moneytech/ZX1541-Interface/files_found_on_the_internet/Pictures/0001a.jpg

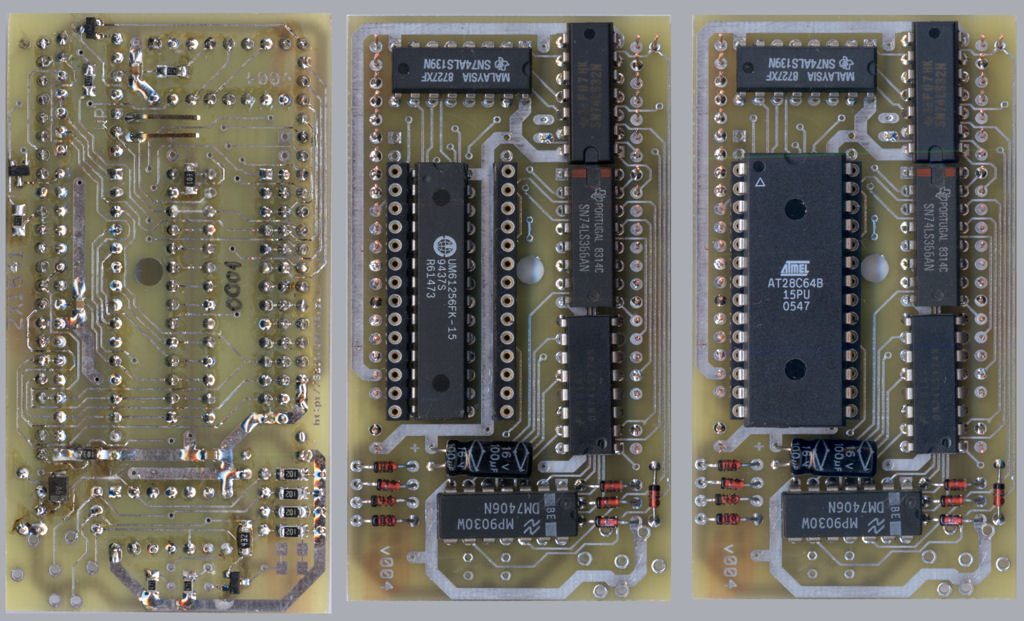
files_found_on_the_internet/Pictures/0001a.jpg
