moneytech/ZX1541-Interface/files_found_on_the_internet/Pictures/0003b.jpg

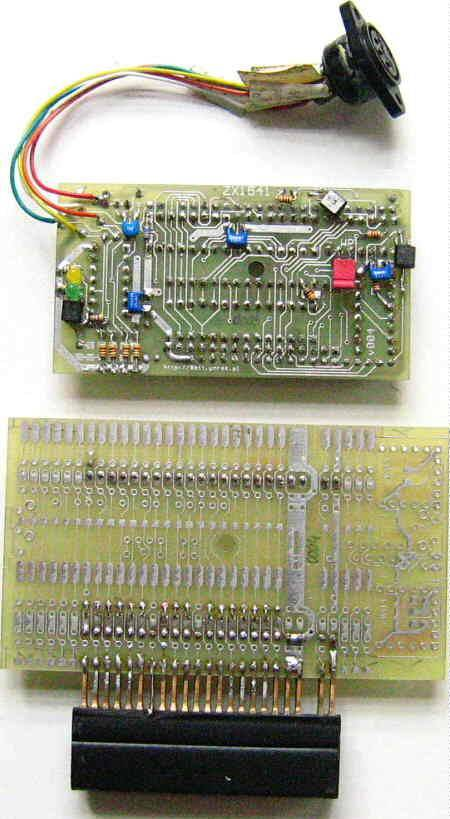
files_found_on_the_internet/Pictures/0003b.jpg
