moneytech/ZX1541-Interface/files_found_on_the_internet/Pictures/1500MEM1.GIF

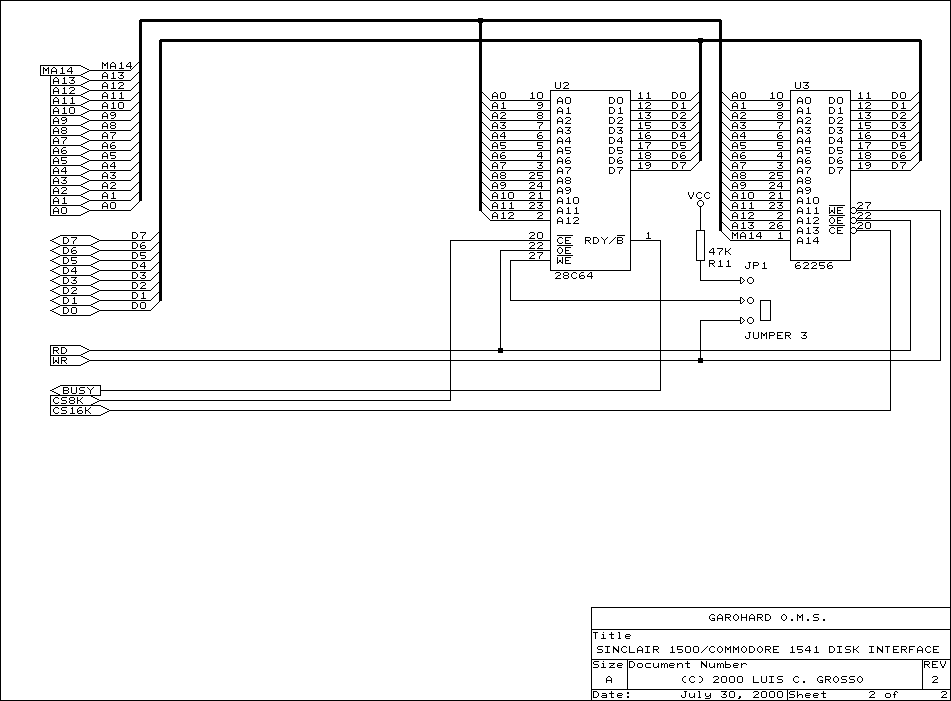
files_found_on_the_internet/Pictures/1500MEM1.GIF
