moneytech/ZX1541-Interface/files_found_on_the_internet/Pictures/disk1.jpg

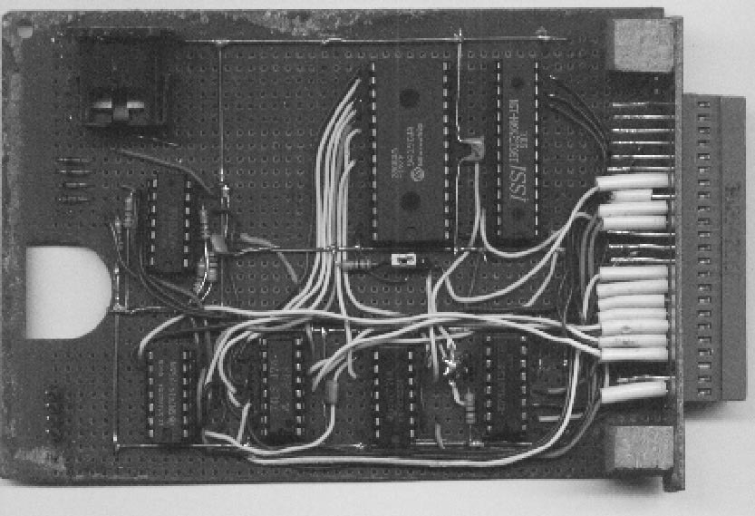
files_found_on_the_internet/Pictures/disk1.jpg
