moneytech/ZX1541-Interface/files_found_on_the_internet/Pictures/disk2.jpg

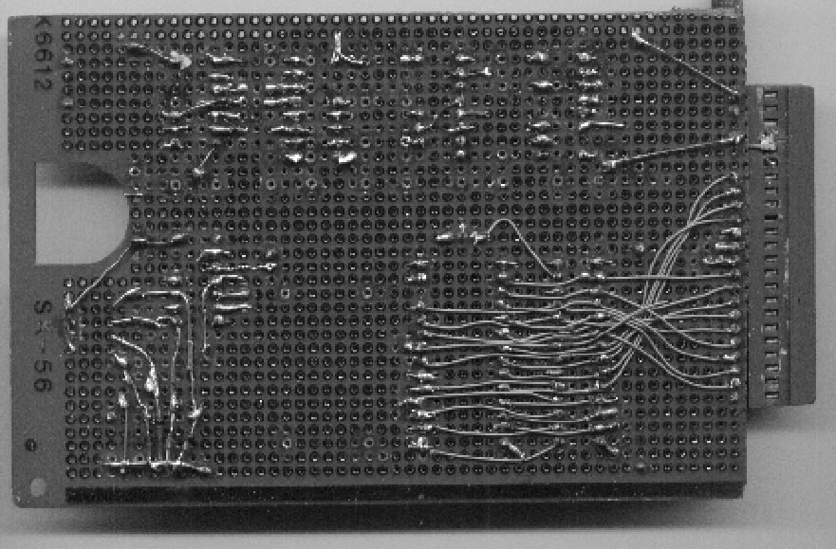
files_found_on_the_internet/Pictures/disk2.jpg
