moneytech/ZX1541-Interface/files_found_on_the_internet/Pictures/ZX1541 SMD PCB New.png

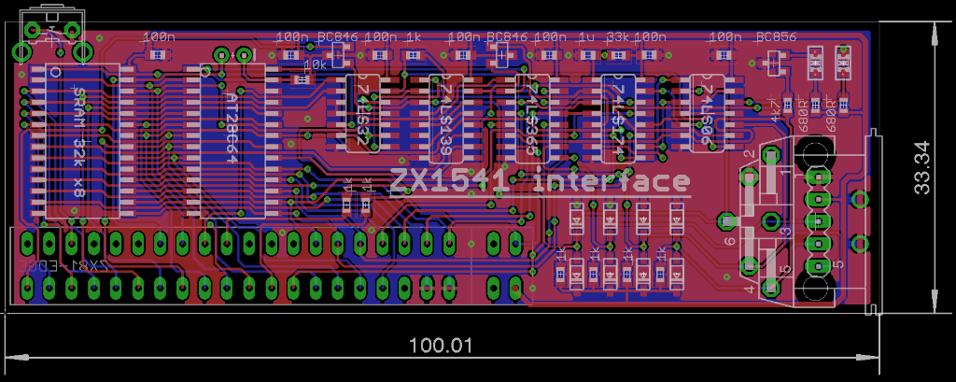
files_found_on_the_internet/Pictures/ZX1541 SMD PCB New.png
