moneytech/ZX1541-Interface/Pics/PCB.jpg

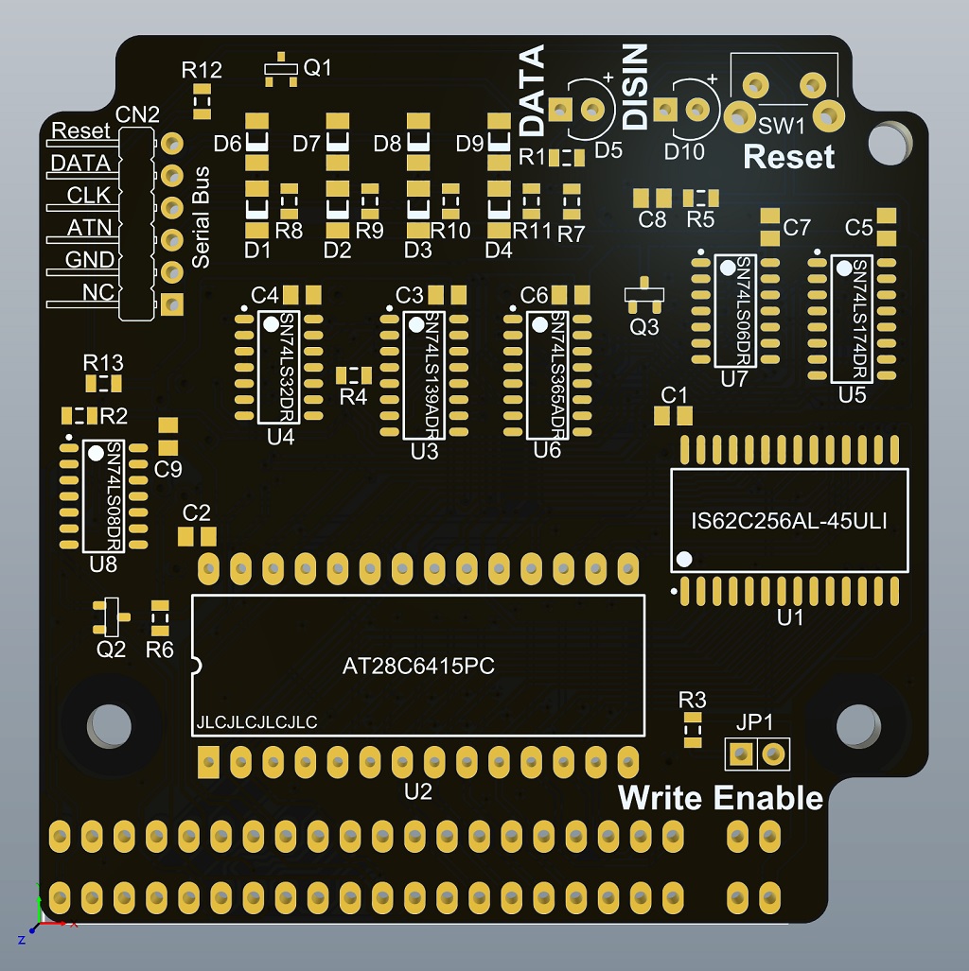
Pics/PCB.jpg
