moneytech/ZX1541-Interface/Pics/PCB_front.jpg

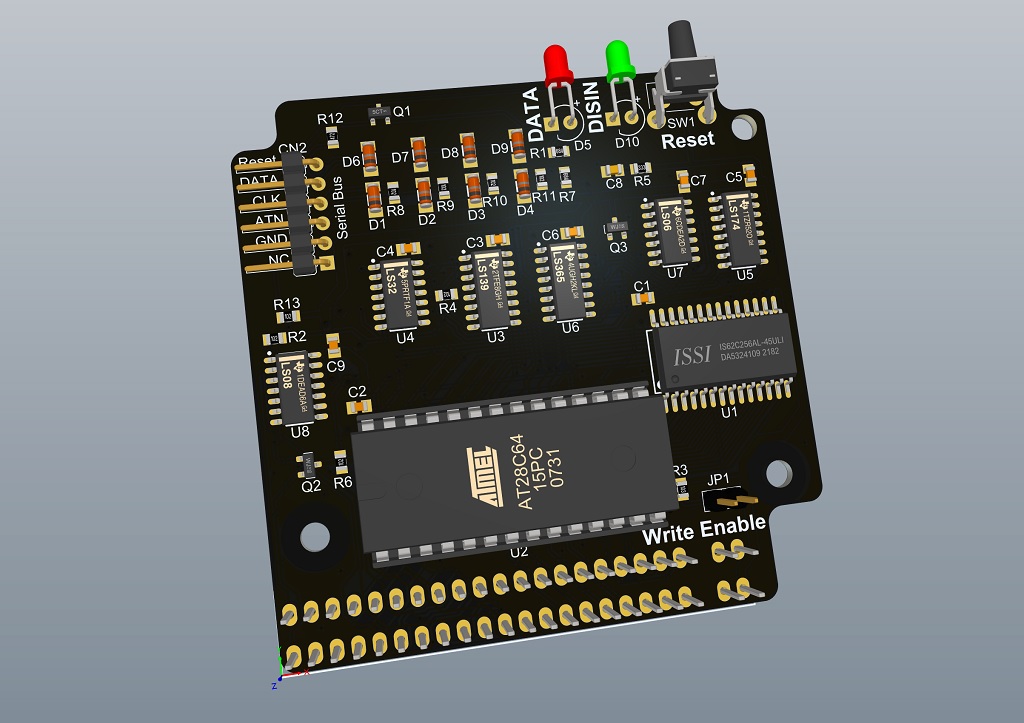
Pics/PCB_front.jpg
